KunaiGC/KunaiGC/images/howdoesitwork/howitworks.PNG

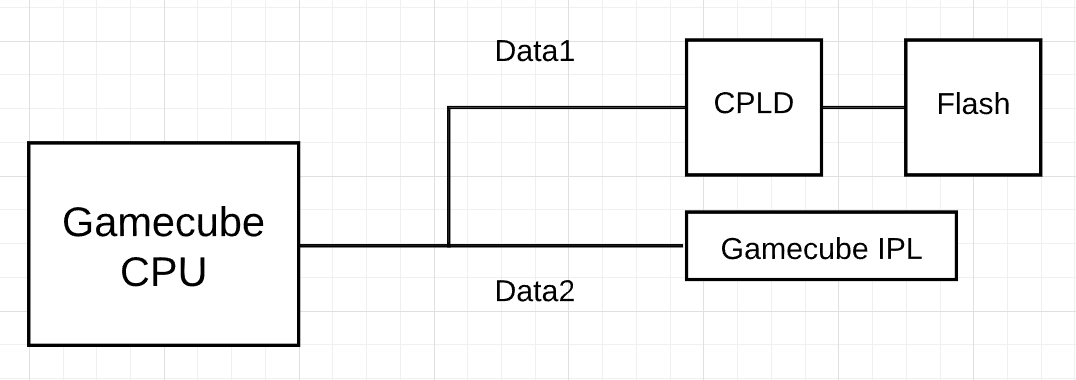
images/howdoesitwork/howitworks.PNG
