KunaiGC/KunaiGC/images/KunaiGC_wip.png

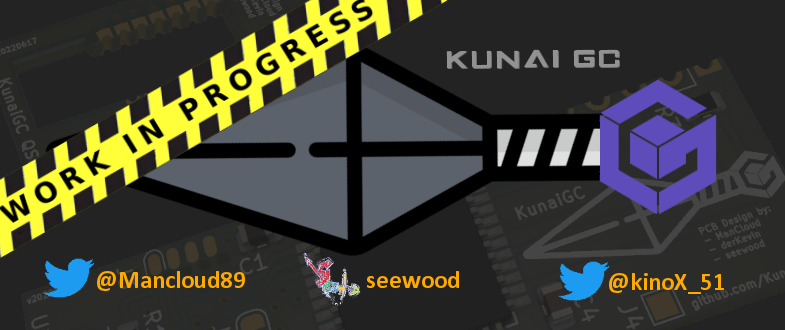
images/KunaiGC_wip.png
