KunaiGC/KunaiGC/images/KunaiUpdater/KunaiUpdater_loading.png

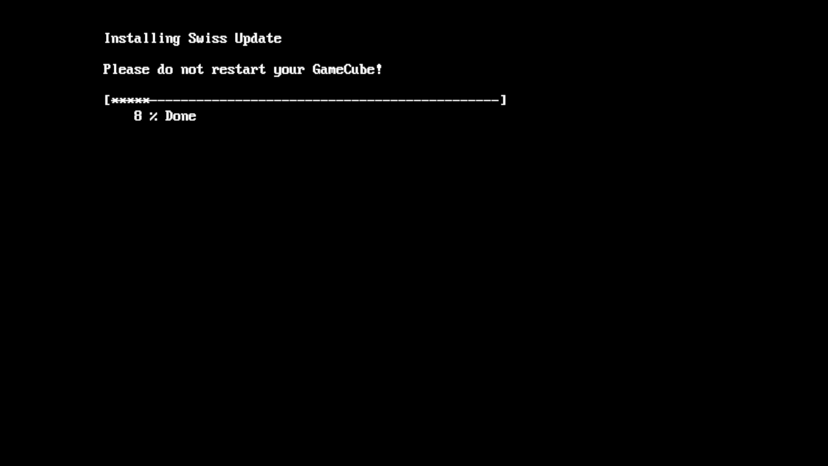
images/KunaiUpdater/KunaiUpdater_loading.png
