KunaiGC/KunaiGC/images/KunaiUpdater/KunaiUpdater_menu.png

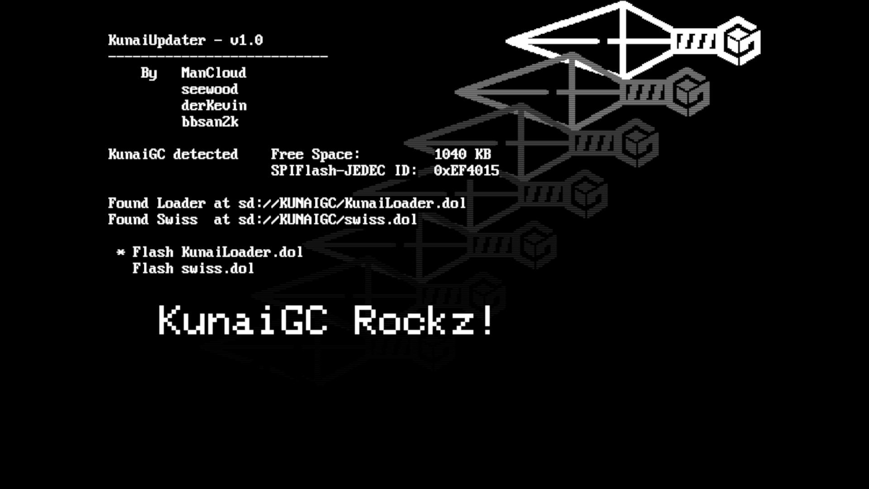
images/KunaiUpdater/KunaiUpdater_menu.png
