KunaiGC/KunaiGC/images/KunaiUpdater/KunaiUpdater_menu_2.png

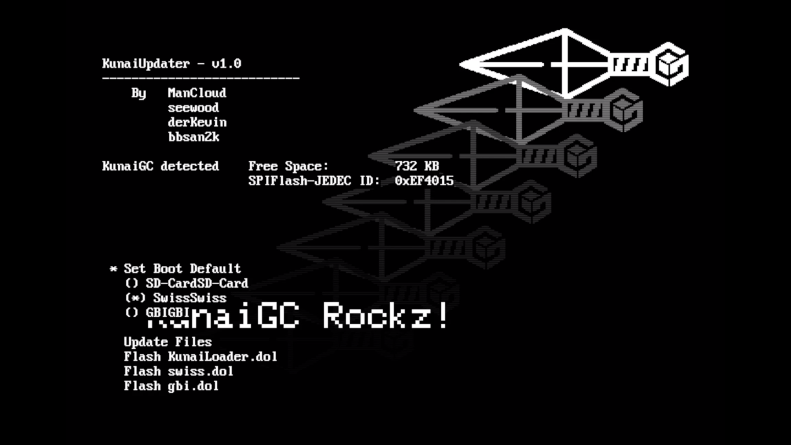
images/KunaiUpdater/KunaiUpdater_menu_2.png
