KunaiGC/KunaiGC/images/programcpld/Diagram_cpld.jpg

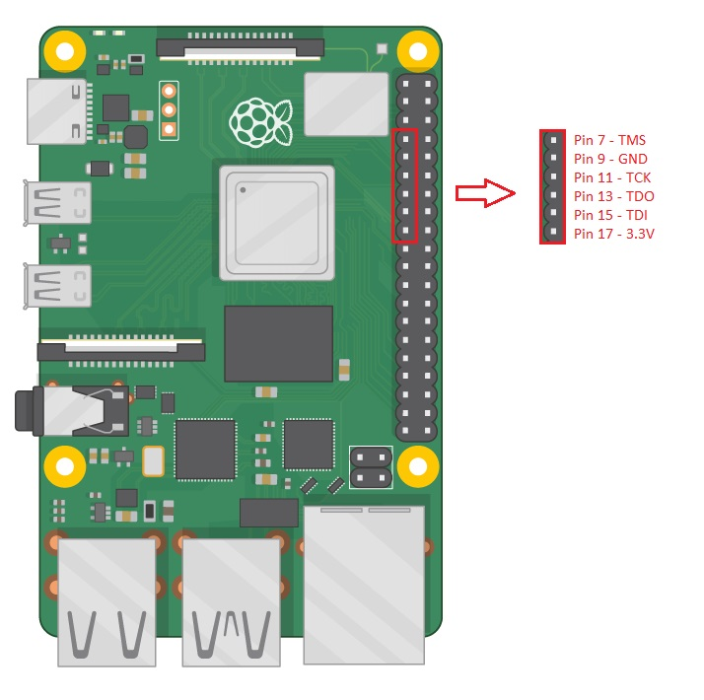
images/programcpld/Diagram_cpld.jpg
