KunaiGC/KunaiGC/images/programcpld/raspi_soicbite.jpg

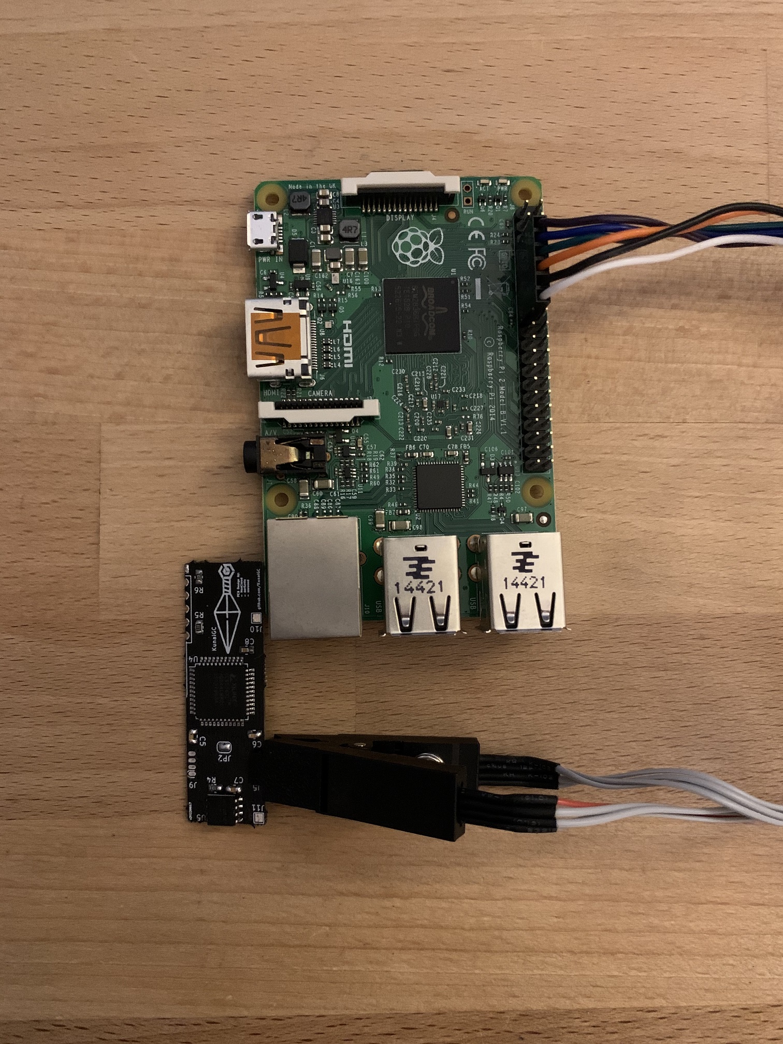
images/programcpld/raspi_soicbite.jpg
