KunaiGC/KunaiGC/images/programcpld/soicbite-pinout.jpg

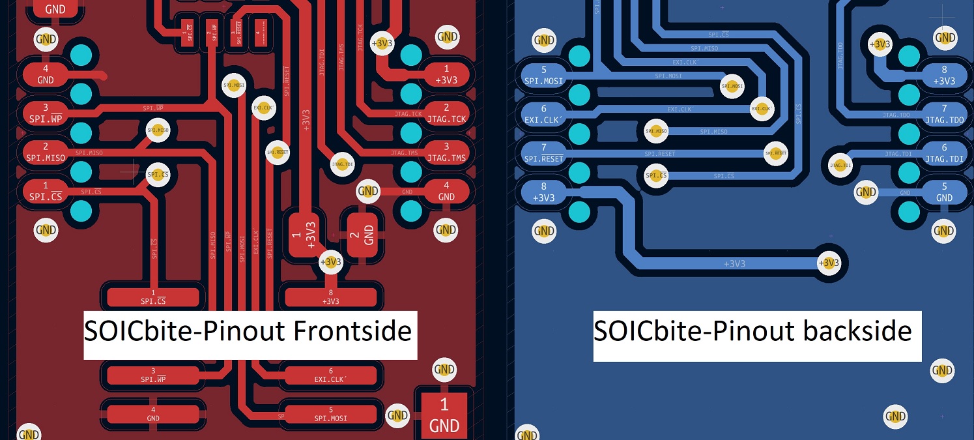
images/programcpld/soicbite-pinout.jpg
