KunaiGC/KunaiGC/images/programflash/Diagram_flashrom.jpg

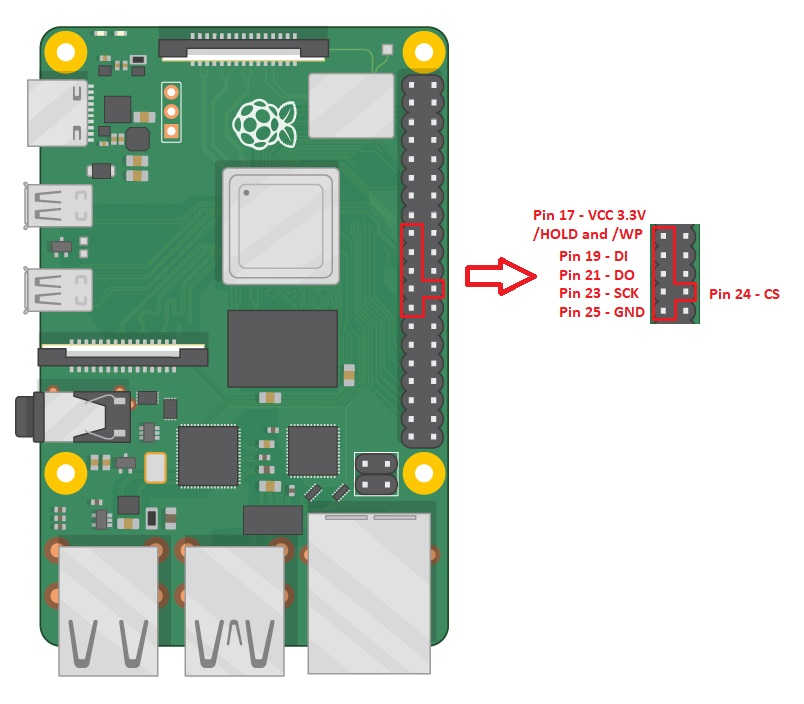
images/programflash/Diagram_flashrom.jpg
