KunaiGC/KunaiGC/images/programflash/program_flash.jpg

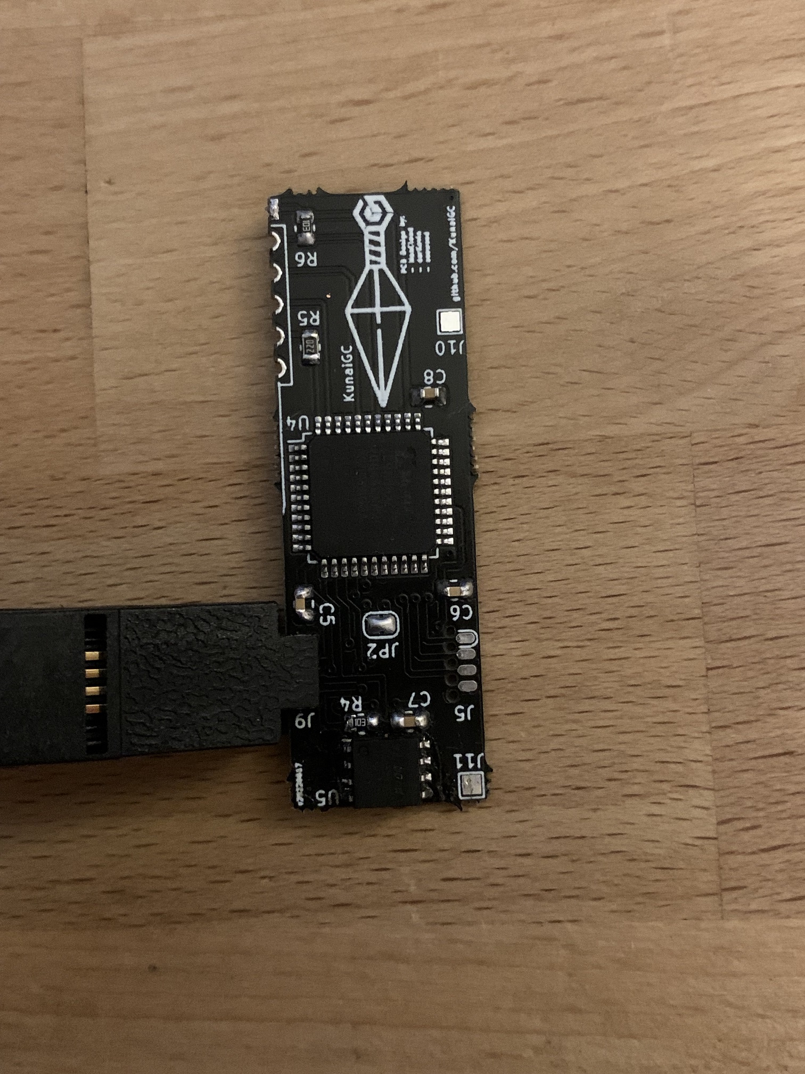
images/programflash/program_flash.jpg
