KunaiGC/KunaiGC/images/soicbite_filed.jpg

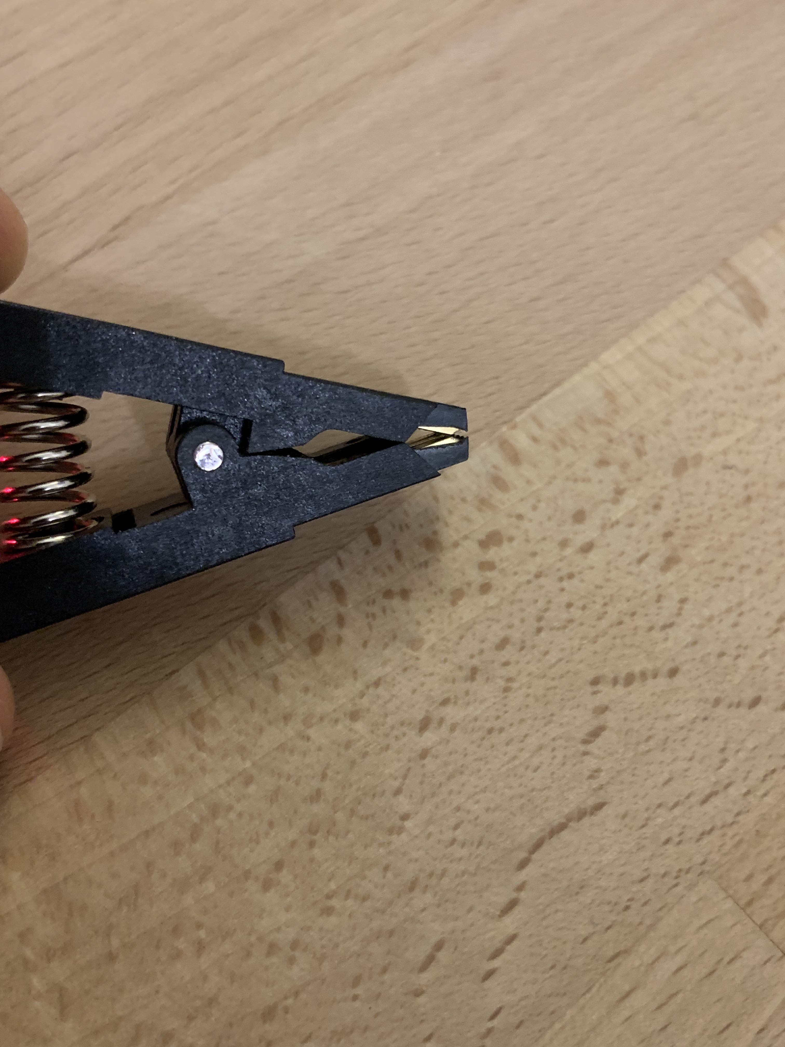
images/soicbite_filed.jpg
