KunaiGC/KunaiGC/images/programcpld/raspi_wiring.jpg

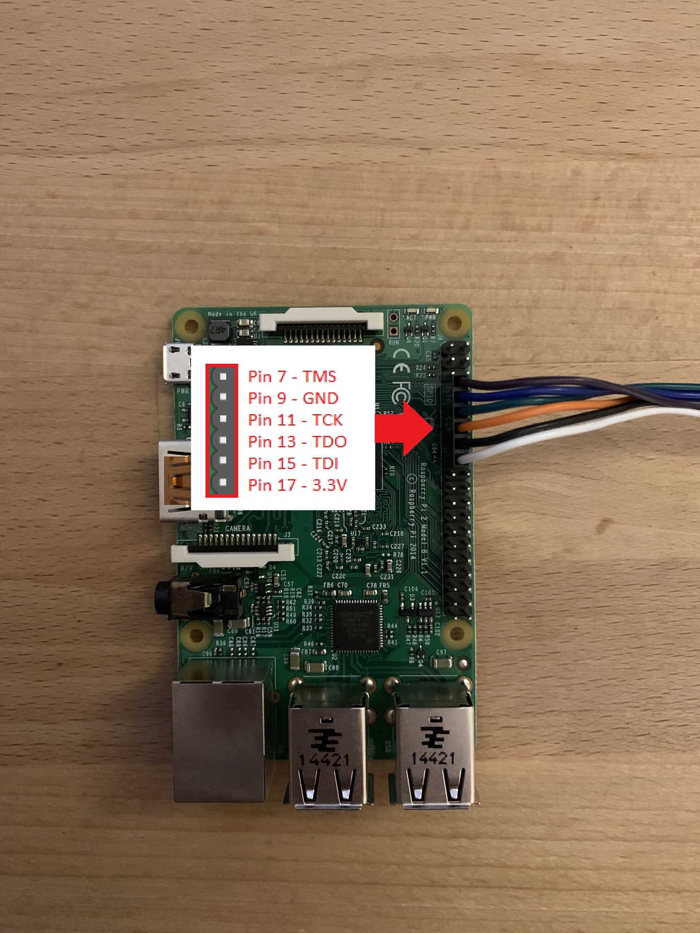
images/programcpld/raspi_wiring.jpg
