KunaiGC/KunaiGC/images/solderkunai/alligned_kunai.jpg

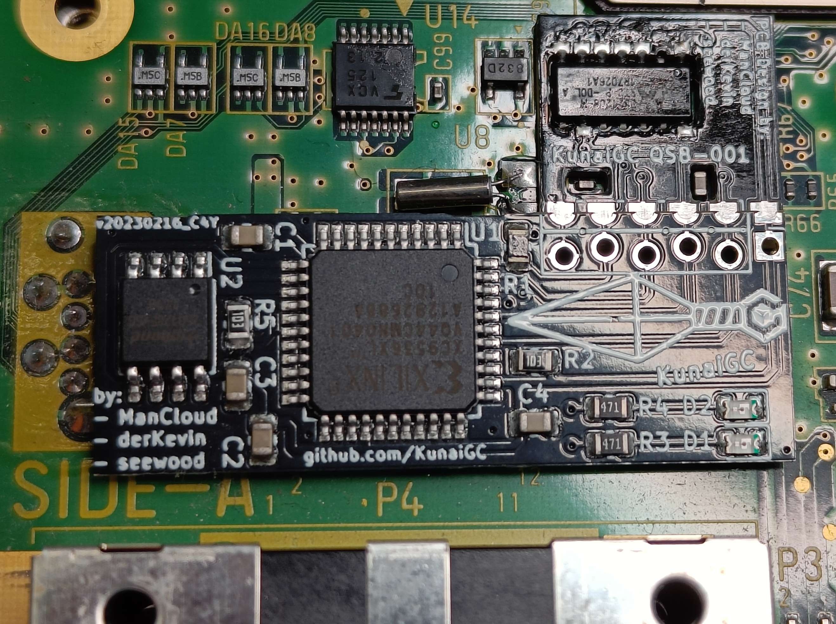
images/solderkunai/alligned_kunai.jpg
