KunaiGC/KunaiGC/images/solderkunai/betaunits/kunaigc_assembled.jpg

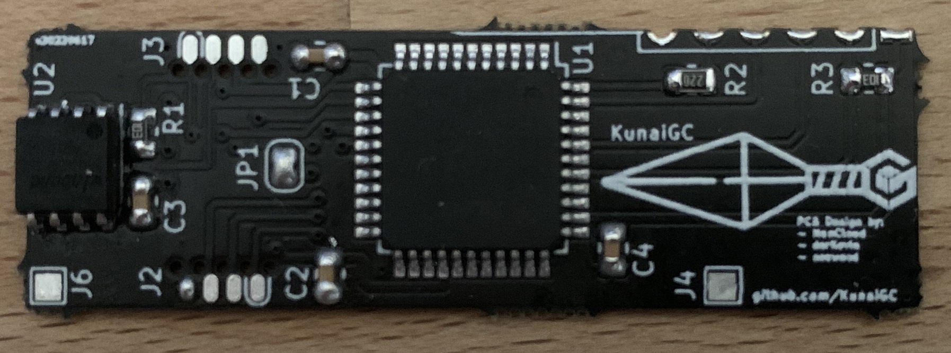
images/solderkunai/betaunits/kunaigc_assembled.jpg
