KunaiGC/KunaiGC/images/solderkunai/betaunits/kunaigc_soldered_w_heatsink.jpg

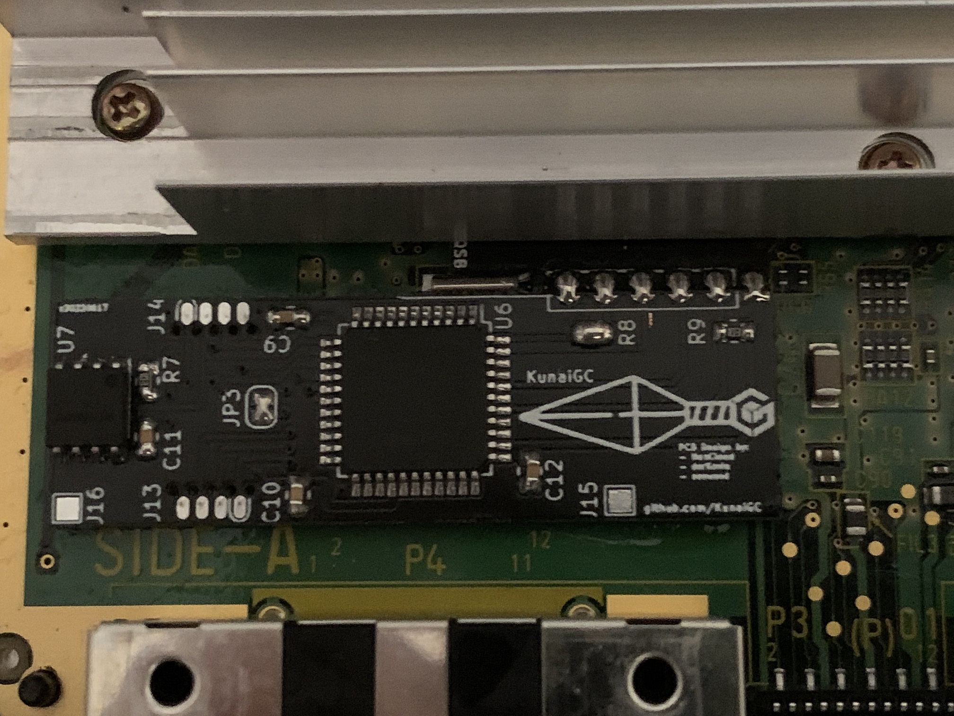
images/solderkunai/betaunits/kunaigc_soldered_w_heatsink.jpg
