KunaiGC/KunaiGC/images/solderkunai/betaunits/kunaigc_soldered_wo_heatsink.jpg

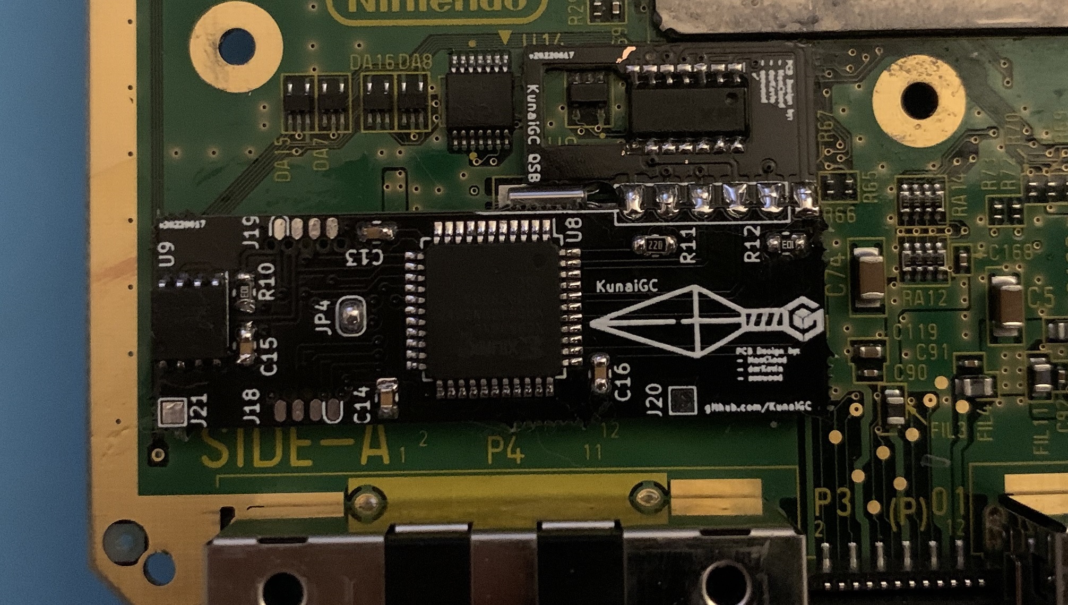
images/solderkunai/betaunits/kunaigc_soldered_wo_heatsink.jpg
