KunaiGC/KunaiGC/images/solderkunai/kunai_back.jpg

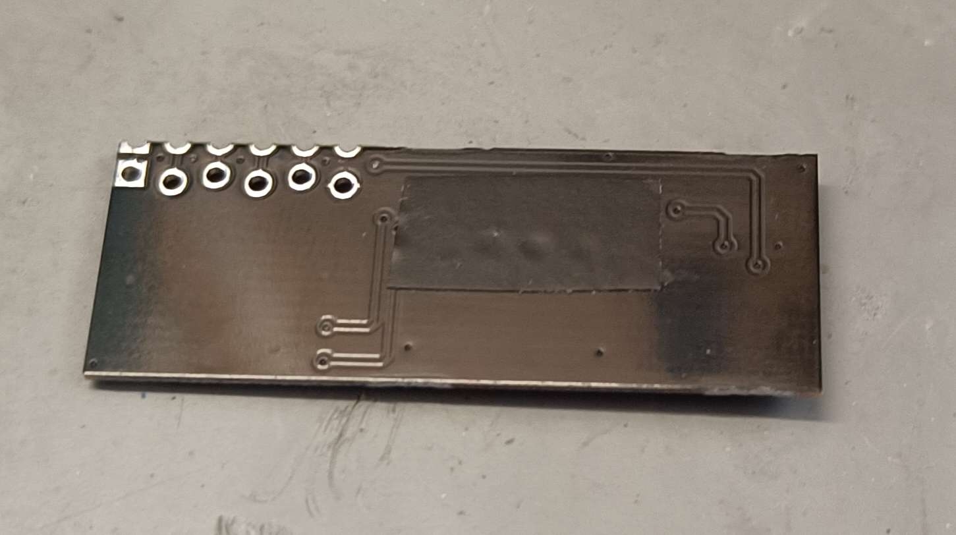
images/solderkunai/kunai_back.jpg
