KunaiGC/KunaiGC/images/solderkunai/qsb_allignment.jpg

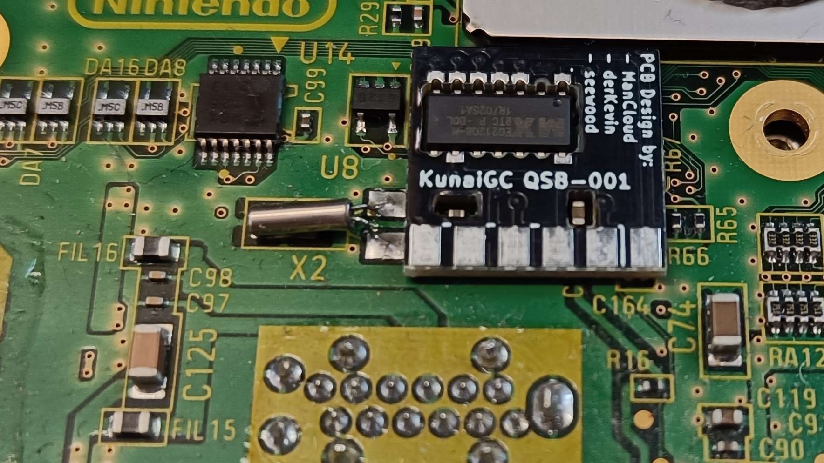
images/solderkunai/qsb_allignment.jpg
