KunaiGC/KunaiGC/images/solderkunai/solder_kunai.jpg

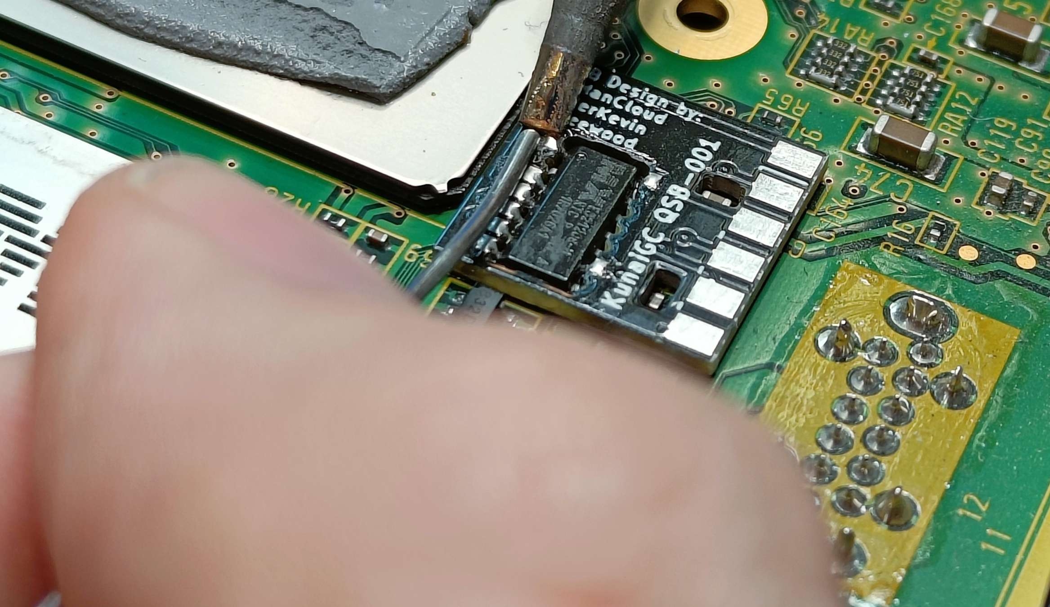
images/solderkunai/solder_kunai.jpg
