KunaiGC/KunaiGC/images/solderkunai/soldered_kunai.jpg

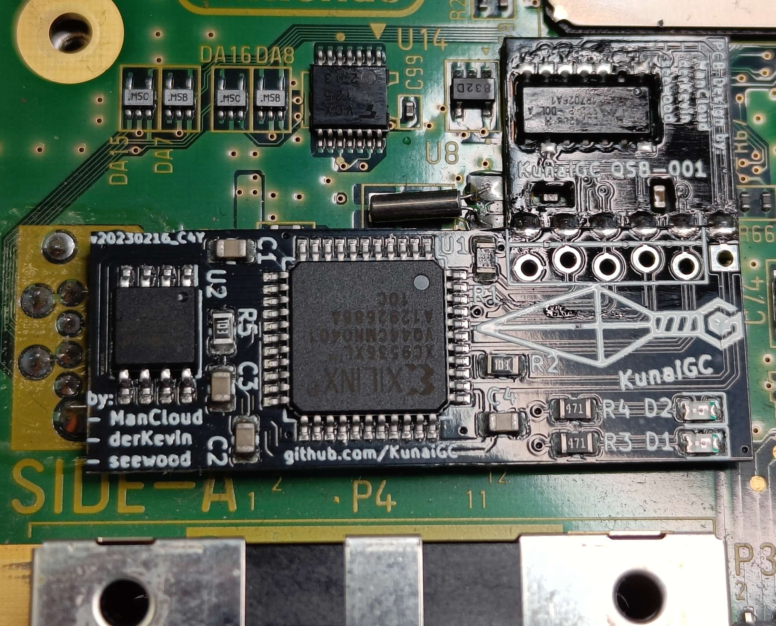
images/solderkunai/soldered_kunai.jpg
