KunaiGC/KunaiGC/images/testusingkunai/Kunai_Controller_Manual_final.png

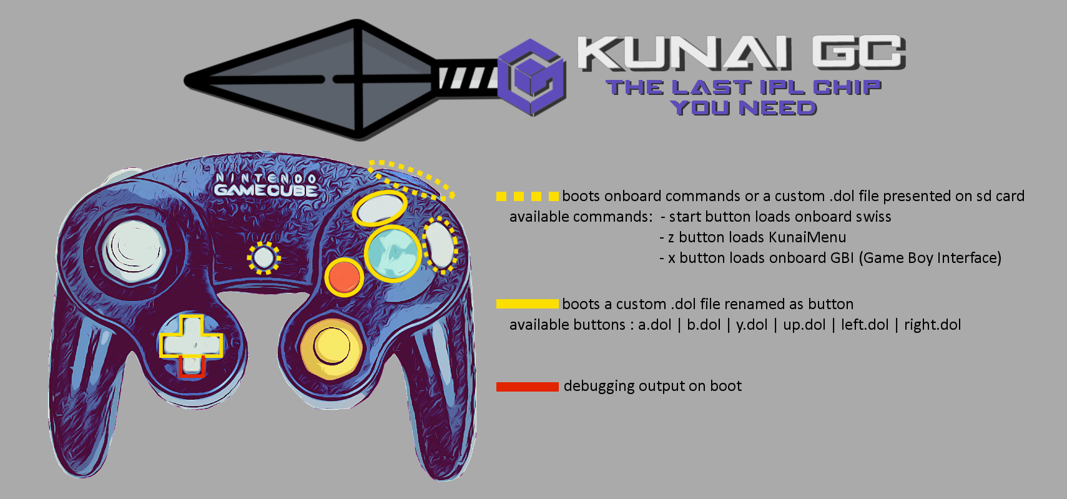
images/testusingkunai/Kunai_Controller_Manual_final.png
