KunaiGC/KunaiGC/images/testpoints_1.jpg

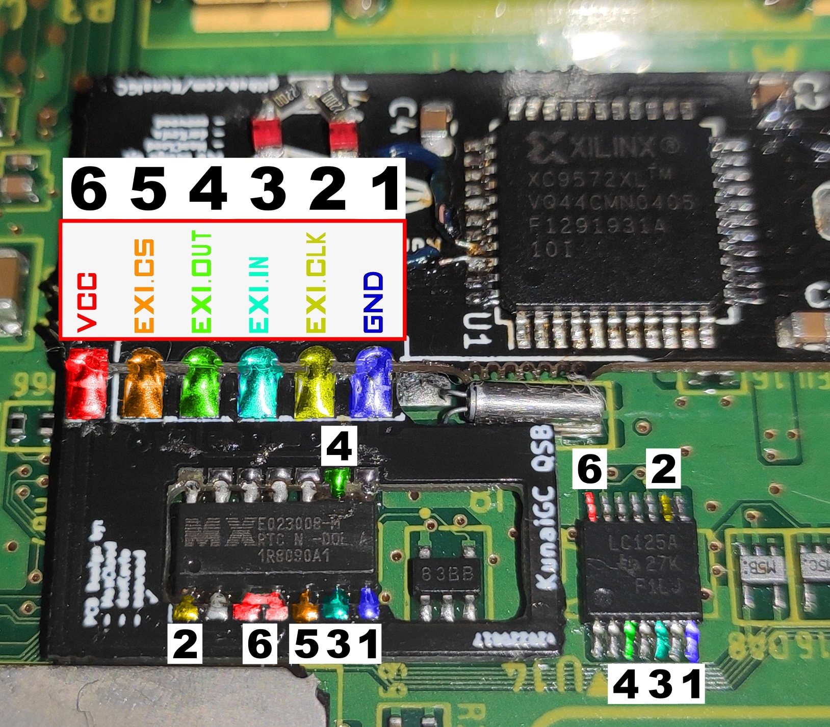
images/testpoints_1.jpg
