KunaiGC/KunaiGC/images/testpoints_2.jpg

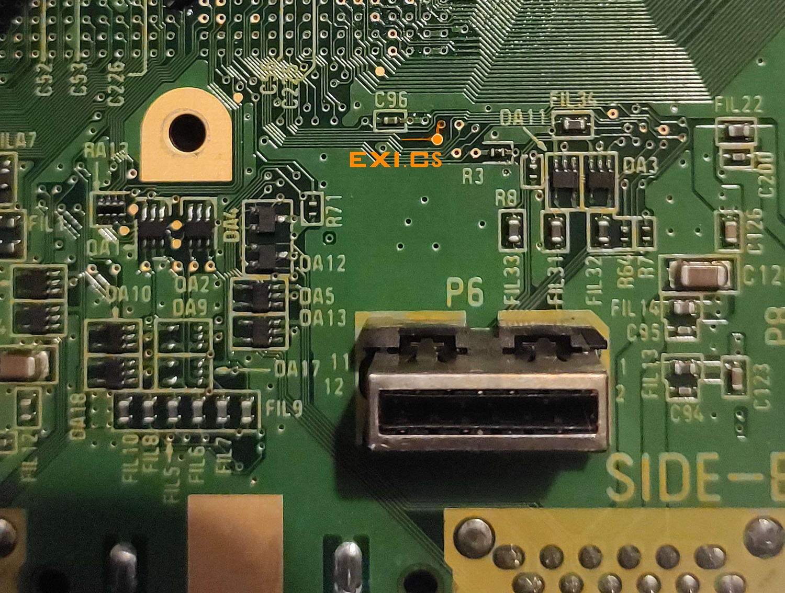
images/testpoints_2.jpg
