KunaiGC/KunaiGC/images/testusingkunai/start_swiss.jpg

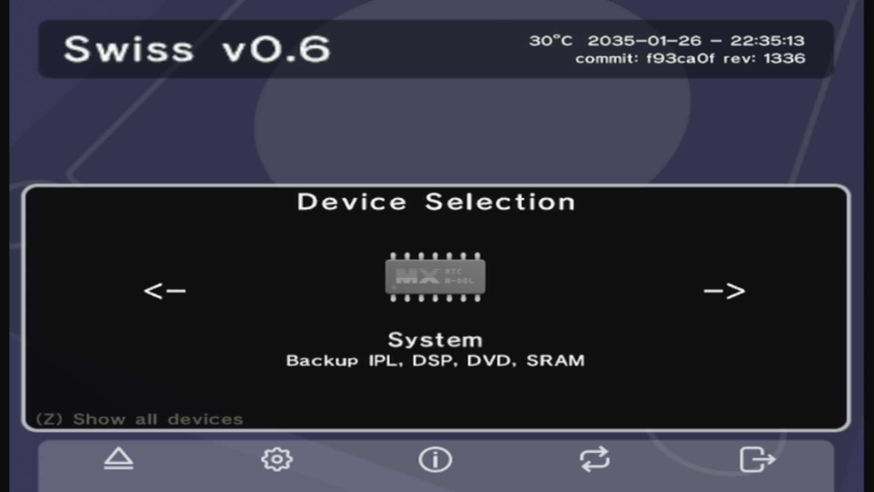
images/testusingkunai/start_swiss.jpg
