KunaiGC/KunaiGC/images/testusingkunai/swiss_igr.png

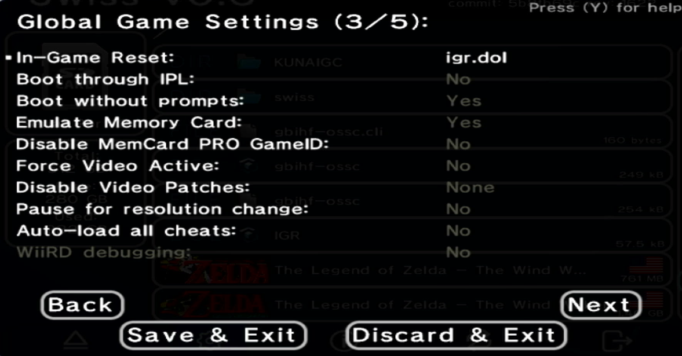
images/testusingkunai/swiss_igr.png
