KunaiGC/KunaiGC/images/testusingkunai/zbutton.png

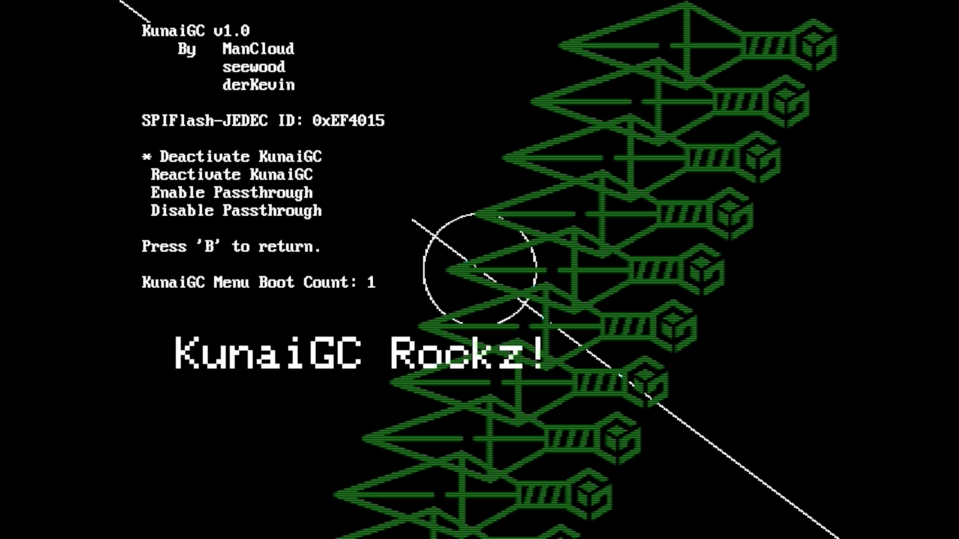
images/testusingkunai/zbutton.png
