KunaiGC/KunaiGC/KunaiLoader/source/kunaigc/kunaigc.c

/*
 * kunaigc.c
 *
 *  Created on: Jul 11, 2022
 *      Author: mancloud
 */


#include "kunaigc.h"

// variables used by the filesystem
lfs_t lfs;
lfs_file_t lfs_file;

// configuration of the filesystem is provided by this struct
const struct lfs_config cfg = {
    // block device operations
    .read  = kunai_read,
    .prog  = kunai_write,
    .erase = kunai_erase,
    .sync  = kunai_sync,

    // block device configuration
    .read_size = 4,
    .prog_size = W25Q80BV_PAGE_SIZE,
    .block_size = 4096,
    .block_count = 448,
    .cache_size = W25Q80BV_PAGE_SIZE*8,
    .lookahead_size = 16,
    .block_cycles = 500,
};

int kunai_load_payload(u32 addr, size_t size){
    kprintf("Trying loading from internal Memory");
    int res = 1;
    addr <<= 6;

    EXI_Lock(EXI_CHANNEL_0, EXI_DEVICE_1, NULL);
    EXI_Select(EXI_CHANNEL_0, EXI_DEVICE_1, EXI_SPEED16MHZ);
    EXI_Imm(EXI_CHANNEL_0, &addr, 4, EXI_WRITE, NULL);
    EXI_Sync(EXI_CHANNEL_0);
    EXI_Imm(EXI_CHANNEL_0, &size, 4, EXI_READ, NULL);
    EXI_Sync(EXI_CHANNEL_0);
    dol_alloc(size);
    if(!dol)
    {
        res = 0;
        goto end;
    }
    kprintf("Receiving file...\n");
    unsigned char* pointer = dol;
    while(size--){
        EXI_Imm(EXI_CHANNEL_0, pointer++, 1, EXI_READ, NULL);
        EXI_Sync(EXI_CHANNEL_0);
    }
    end:
    EXI_Deselect(EXI_CHANNEL_0);
    EXI_Unlock(EXI_CHANNEL_0);
    return res;
}

//wait for "WIP" flag being unset
void kunai_wait() {
        usleep(150000);
        kunai_enable_passthrough();
        spiflash_wait();
        kunai_disable_passthrough();
}

void kunai_disable_passthrough(void) {
    EXI_Deselect(EXI_CHANNEL_0);
    EXI_Unlock(EXI_CHANNEL_0);
//  usleep(75000);
}

void kunai_enable_passthrough(void) {
    s32 retVal = 0;
    uint8_t repetitions = 3;
    do {
        u32 addr = 0x80000000; //for passthrough we need to send one '1' and 31 '0' and afterwards whatever we want
        EXI_Lock(EXI_CHANNEL_0, EXI_DEVICE_1, NULL);
        EXI_Select(EXI_CHANNEL_0, EXI_DEVICE_1, EXI_SPEED32MHZ);
        EXI_Imm(EXI_CHANNEL_0, &addr, 4, EXI_WRITE, NULL);
        retVal = EXI_Sync(EXI_CHANNEL_0);
    } while(retVal <= 0 && --repetitions);
}



uint32_t kunai_get_jedecID(void) {
    uint32_t jedecID = 0;
    kunai_reenable();
    kunai_enable_passthrough();
    jedecID = spiflash_jedec_id();
    kunai_disable_passthrough();
    kunai_disable();
    return jedecID;
}

int kunai_read(const struct lfs_config *c, lfs_block_t block, lfs_off_t off, void *buffer, lfs_size_t size) {
    int retVal = 0;
    if(size) {
        uint32_t * p_data = buffer;
        kunai_reenable();
        kunai_enable_passthrough();
        spiflash_read_start_fast((block * c->block_size) + off + KUNAI_OFFS);
        for(lfs_size_t i = size; i > 0; i-=(c->read_size)){
          *(p_data++) = spiflash_read_uint32();
        }
        kunai_disable_passthrough();
        kunai_disable();
    } else {
        retVal = LFS_ERR_IO;
    }

    return retVal;
}

int kunai_write(const struct lfs_config *c, lfs_block_t block, lfs_off_t off, const void *buffer, lfs_size_t size) {
    int retVal = 0;
    if(size) {
        uint32_t * p_data = (uint32_t *) buffer;
        kunai_reenable();

        for(lfs_size_t i = size; i > 0; i -= c->prog_size) {

            kunai_enable_passthrough();
            spiflash_write_enable();
            kunai_disable_passthrough();

            kunai_enable_passthrough();
            spiflash_cmd_addr_start(W25Q80BV_CMD_PAGE_PROG, (block * c->block_size) + KUNAI_OFFS + off);
            for(uint8_t ii = 0; ii < (W25Q80BV_PAGE_SIZE/4); ii++) {
                spiflash_write_uint32(*p_data);
                p_data++;
            }
            kunai_disable_passthrough();
            kunai_wait();
            off += c->prog_size;
        }
        kunai_disable();
    } else {
        retVal = LFS_ERR_IO;
    }
    return retVal;
}

int kunai_erase(const struct lfs_config *c, lfs_block_t block) {
    int retVal = 0;
    kunai_reenable();
    kunai_sector_erase(block * c->block_size + KUNAI_OFFS);
    kunai_disable();
    return retVal;
}

int kunai_sync(const struct lfs_config *c) { return 0;}

void kunai_disable(void) {
    u32 addr = 0xc0000000;
    u32 data = 6 << 24;
    EXI_Lock(EXI_CHANNEL_0, EXI_DEVICE_1, NULL);
    EXI_Select(EXI_CHANNEL_0, EXI_DEVICE_1, EXI_SPEED8MHZ);
    EXI_Imm(EXI_CHANNEL_0, &addr, 4, EXI_WRITE, NULL);
    EXI_Sync(EXI_CHANNEL_0);
    EXI_Imm(EXI_CHANNEL_0, &data, 4, EXI_WRITE, NULL);
    EXI_Sync(EXI_CHANNEL_0);
    EXI_Deselect(EXI_CHANNEL_0);
    EXI_Unlock(EXI_CHANNEL_0);
}

void kunai_reenable(void) {
    u32 addr = 0xc0000000;
    u32 data = 1 << 24;
    EXI_Lock(EXI_CHANNEL_0, EXI_DEVICE_1, NULL);
    EXI_Select(EXI_CHANNEL_0, EXI_DEVICE_1, EXI_SPEED8MHZ);
    EXI_Imm(EXI_CHANNEL_0, &addr, 4, EXI_WRITE, NULL);
    EXI_Sync(EXI_CHANNEL_0);
    EXI_Imm(EXI_CHANNEL_0, &data, 4, EXI_WRITE, NULL);
    EXI_Sync(EXI_CHANNEL_0);
    EXI_Deselect(EXI_CHANNEL_0);
    EXI_Unlock(EXI_CHANNEL_0);
}

void kunai_sector_erase(uint32_t addr) {
    kunai_enable_passthrough();
    spiflash_write_enable();
    kunai_disable_passthrough();
    kunai_enable_passthrough();
    spiflash_cmd_addr_start(W25Q80BV_CMD_ERASE_4K, addr);
    kunai_disable_passthrough();
    kunai_wait();
}
